kaviles22/EMG_SignalClassification/src/real_time/modeldata.h

#ifndef PROSTHETIC_MODEL_DATA_H_
#define PROSTHETIC_MODEL_DATA_H_ //header guard to prevent adding it multiple times

extern const unsigned char prosthetic_model_data[];
extern const int prosthetic_model_data_len;

#endif  // PROSTHETIC_MODEL_DATA_H
